sweetlilmre/Dominator-Parts/reference/cam_v2/own_cam_top_v2.jpg

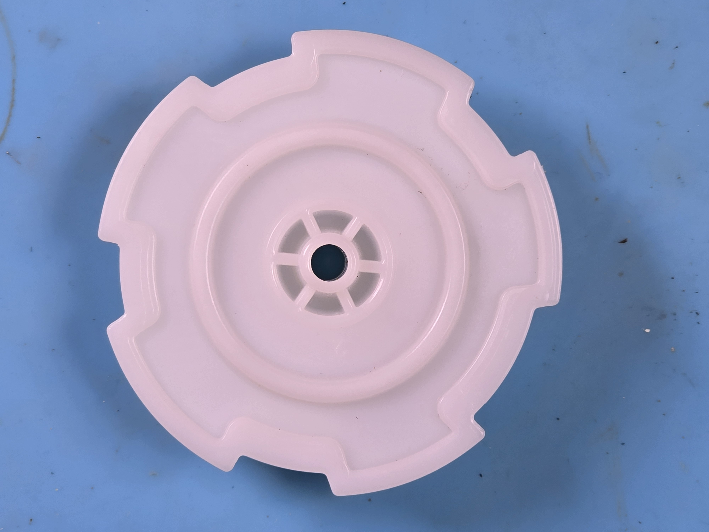
reference/cam_v2/own_cam_top_v2.jpg
