sweetlilmre/Dominator-Parts/reference/cam_v2/own_gear_side_2_v2.jpg

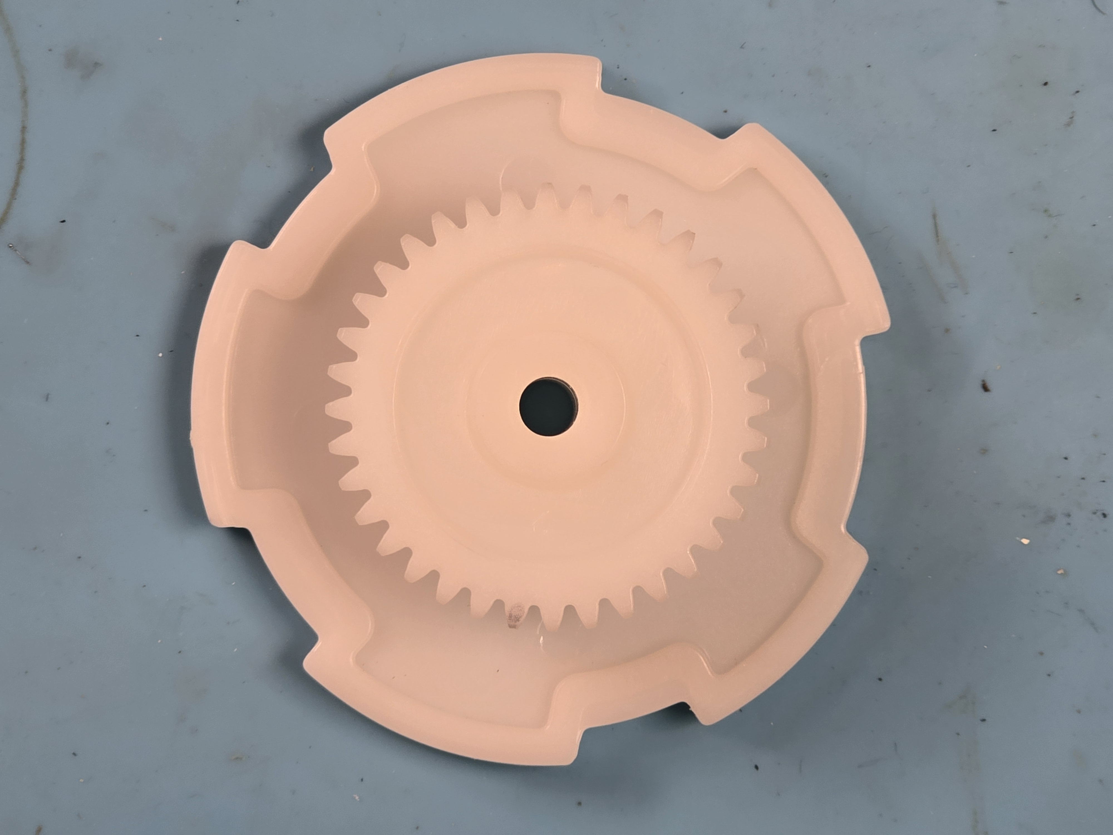
reference/cam_v2/own_gear_side_2_v2.jpg
