sweetlilmre/Dominator-Parts/reference/drive_gears/own_drive_gear_2.jpg

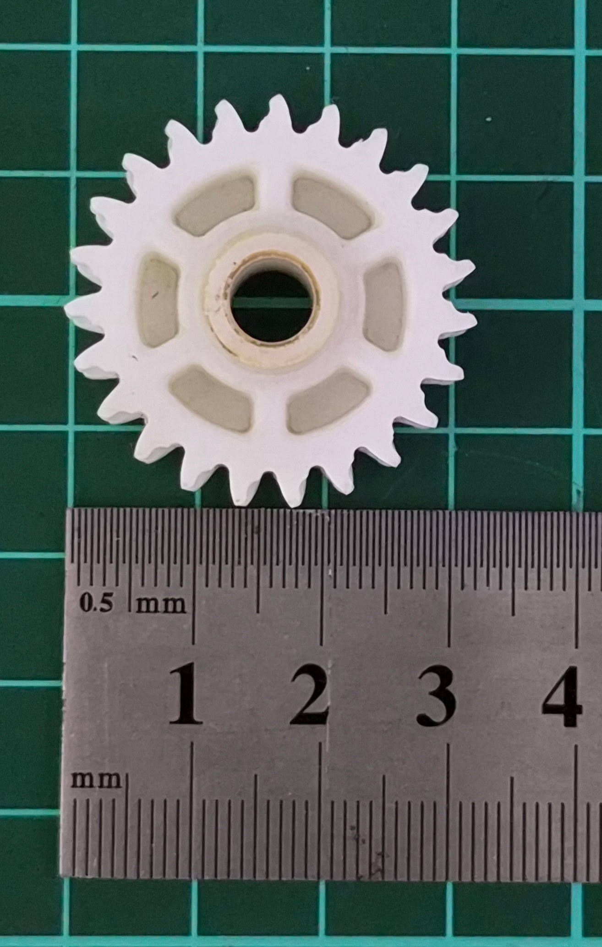
reference/drive_gears/own_drive_gear_2.jpg
