sweetlilmre/Dominator-Parts/reference/drive_gears/own_drive_gear_2_side.jpg

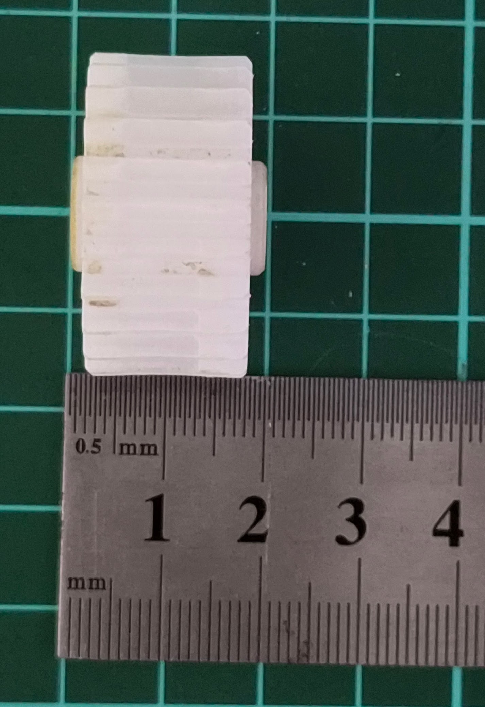
reference/drive_gears/own_drive_gear_2_side.jpg
