sweetlilmre/Dominator-Parts/reference/drive_gears/own_drive_gear_3_top.jpg

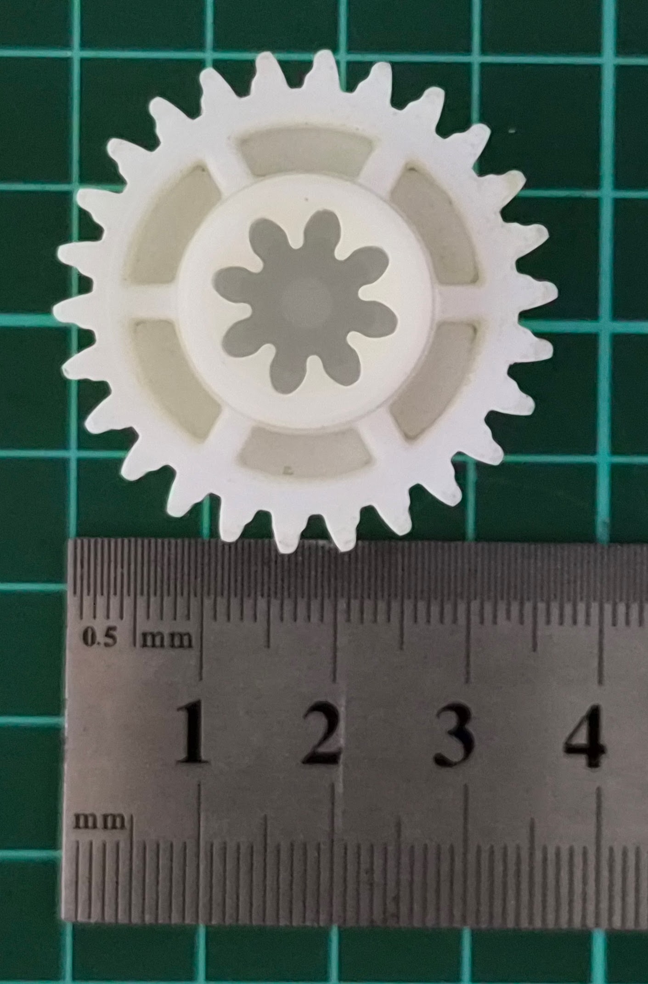
reference/drive_gears/own_drive_gear_3_top.jpg
