sweetlilmre/Dominator-Parts/reference/own_shafts_ruler.jpg

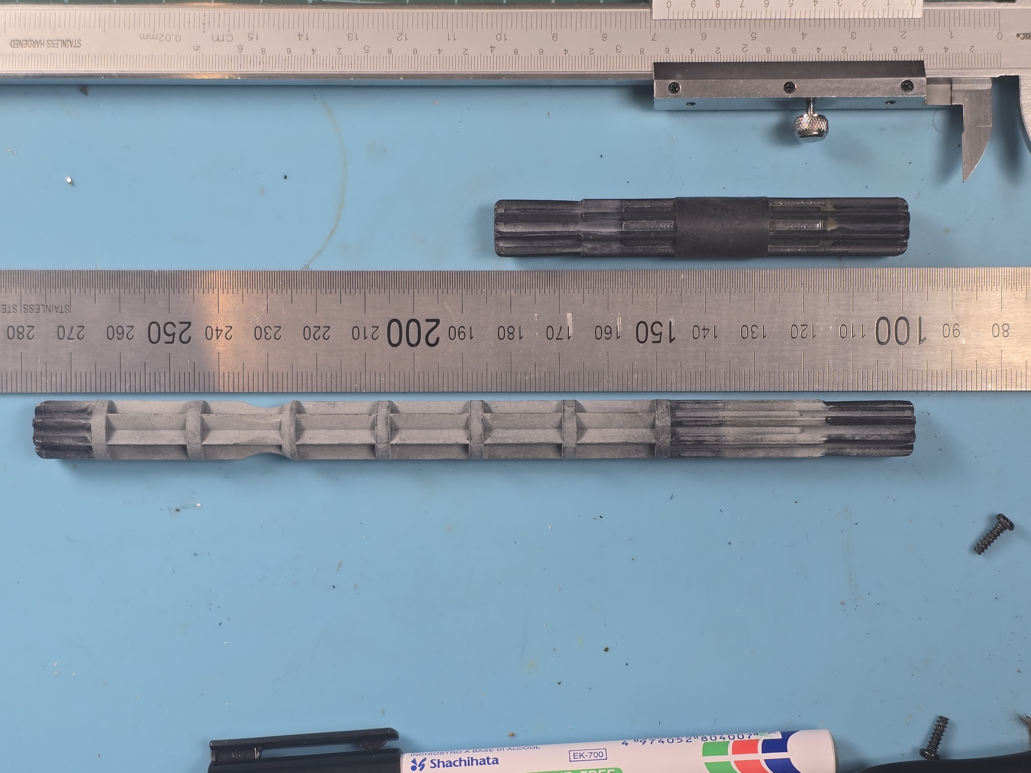
reference/own_shafts_ruler.jpg
