sweetlilmre/Dominator-Parts/renders/shaft_long_flat.png

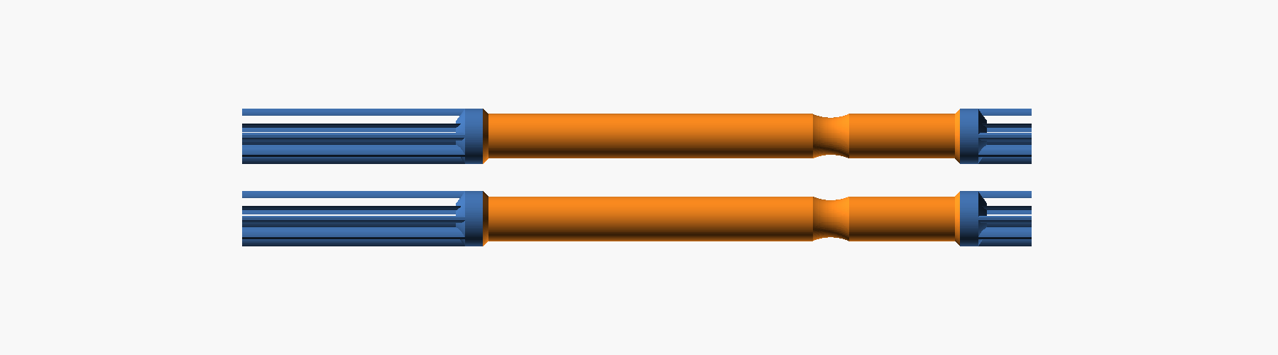
renders/shaft_long_flat.png
