sweetlilmre/Dominator-Parts/renders/shaft_short_end.png

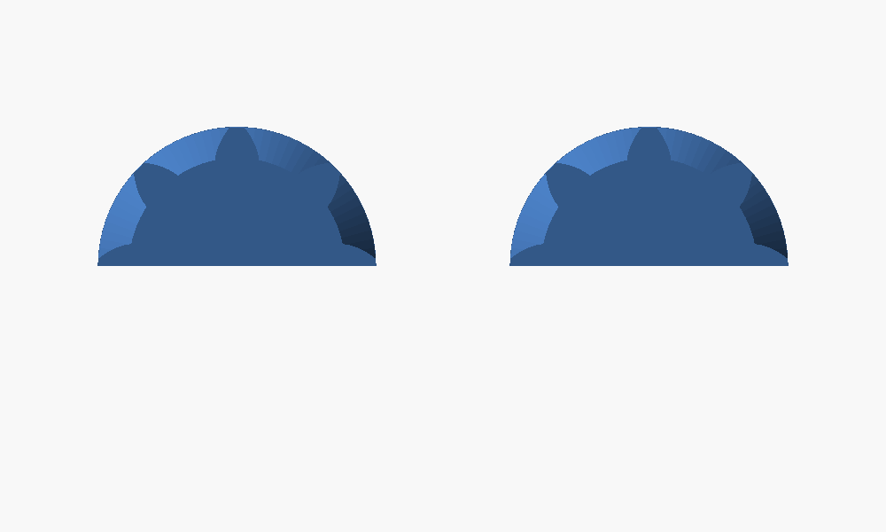
renders/shaft_short_end.png
