sweetlilmre/Dominator-Parts/renders/shaft_short_flat.png

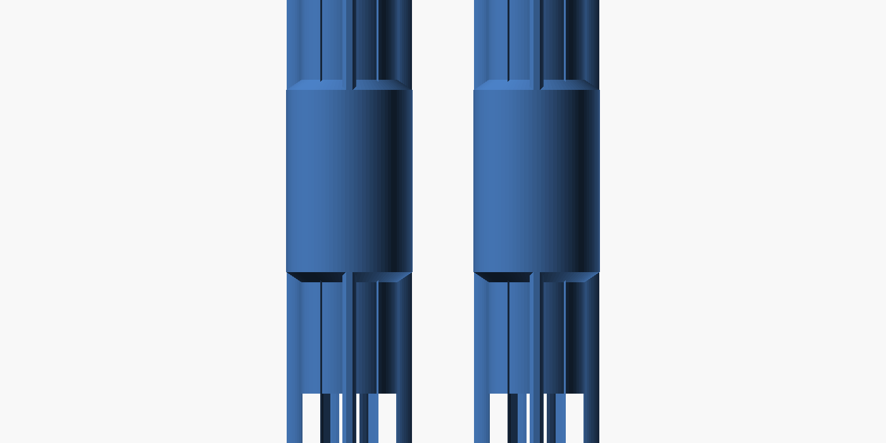
renders/shaft_short_flat.png
