sweetlilmre/Dominator-Parts/stl/dominator_follower.stl

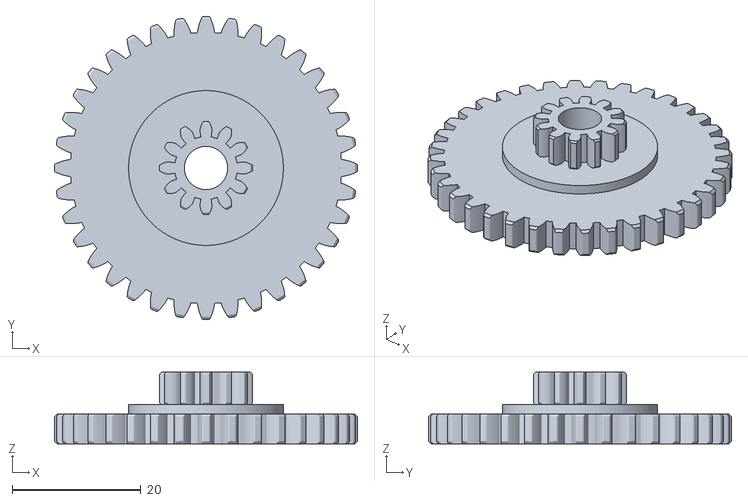
[picture p46: CAD file, 2026-09-06]
stl/dominator_follower.stl
47.0 x 47.0 x 11.1
