sweetlilmre/Dominator-Parts/stl/dominator_washer.stl

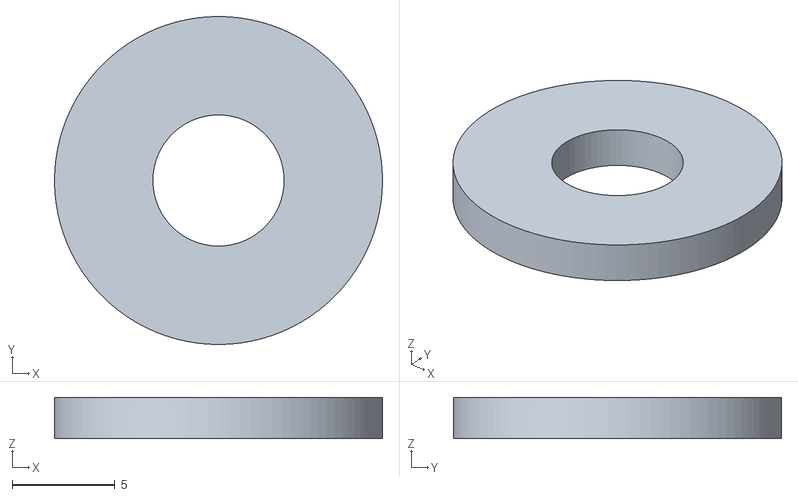
[picture p47: CAD file, 2026-10-06]
stl/dominator_washer.stl
16.0 x 16.0 x 2.00
