sweetlilmre/Dominator-Parts/stl/dominator_cam_v1.stl

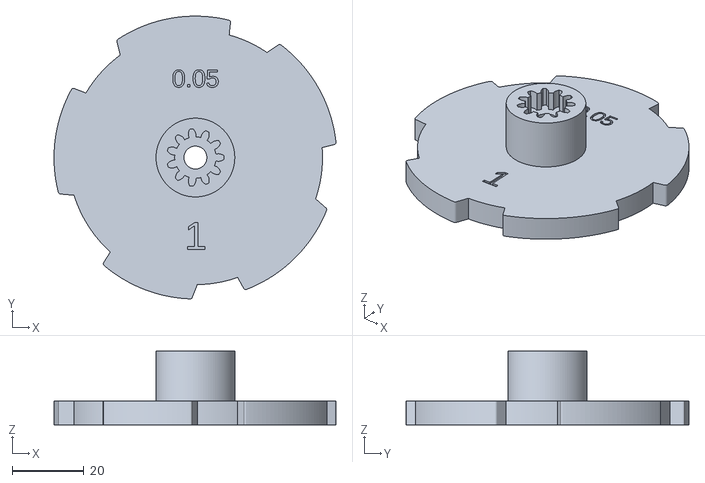
[picture p48: CAD file, 2026-10-06, an earlier design]
stl/dominator_cam_v1.stl
78.8 x 79.0 x 20.6
