sweetlilmre/Dominator-Parts/scad/assembly.scad

// assembly.scad - open this file in OpenSCAD. Use the Customizer panel
// (Window > Customizer) to pick the part and tune every dimension from
// config.scad. Export STLs from here or with render.ps1.
//
//   part = "cam"       flat cam plate with shaft and socket (print as shown)
//   part = "gear"      ring gear with plug, shown plug up for printing
//   part = "washer"    spacer washer
//   part = "reduction_gear"  optional gearbox reduction gear (ring as the gear, plus pinion)
//   part = "assembly"  cam with the gear seated, for checking fit and height
//   part = "shaft_long"   gearbox drive shaft, long
//   part = "shaft_short"  gearbox drive shaft, short
//   part = "drive_gear_1" gearbox drive gear 1, compound 26 T over 19 T
//   part = "drive_gear_2" gearbox drive gear 2, 23 T with a spacer each face
//   part = "drive_gear_3" gearbox drive gear 3, 26 T joining the drive shafts, in two halves
//   part = "cam_rim_modifier"    PrusaSlicer modifier: solid rim band on the cam
//   part = "cam_socket_modifier" PrusaSlicer modifier: solid hub around the cam socket
//   part = "gear_tooth_modifier" PrusaSlicer modifier: solid tooth band on the gear
//   part = "gear_core_modifier"  PrusaSlicer modifier: solid plug on the gear, or pinion on the reduction gear
//   part = "fit_test"  coupon: sockets at several clearances plus loose plugs
//   part = "all"       everything laid out
INVOLUTE_GEAR_NO_DEMO = true;
include <config.scad>
include <cam.scad>
include <cam_gear.scad>
include <reduction_gear.scad>
include <drive_shaft.scad>
include <drive_gear.scad>
include <fit_test.scad>

/* [Part selection] */
part = "all"; // ["all", "cam", "gear", "washer", "reduction_gear", "assembly", "shaft_long", "shaft_short", "drive_gear_1", "drive_gear_2", "drive_gear_3", "fit_test", "cam_rim_modifier", "cam_socket_modifier", "gear_tooth_modifier", "gear_core_modifier"]

module assembled() {
    cam();
    translate([0, 0, shoulder_z()]) cam_gear();
}

if (part == "cam") {
    cam();
} else if (part == "gear") {
    cam_gear_printable();
} else if (part == "washer") {
    spacer_washer();
} else if (part == "reduction_gear") {
    reduction_gear();
} else if (part == "shaft_long") {
    drive_shaft(ds_long);
} else if (part == "shaft_short") {
    drive_shaft(ds_short);
} else if (part == "drive_gear_1") {
    drive_gear_1();
} else if (part == "drive_gear_2") {
    drive_gear_2();
} else if (part == "drive_gear_3") {
    drive_gear_3();
} else if (part == "fit_test") {
    fit_test();
} else if (part == "assembly") {
    assembled();
} else if (part == "cam_rim_modifier") {
    cam_rim_modifier();
} else if (part == "cam_socket_modifier") {
    cam_socket_modifier();
} else if (part == "gear_tooth_modifier") {
    gear_tooth_modifier();
} else if (part == "gear_core_modifier") {
    gear_core_modifier();
} else {
    cam();
    translate([trough_d + 20, 0, 0]) cam_gear_printable();
    translate([trough_d + 20, -(gear_od / 2 + washer_od), 0]) spacer_washer();
    translate([trough_d + 20, gear_od + 8, 0]) reduction_gear();
}

echo(str("gear module = ", gear_module, " mm, pitch dia = ", gear_module * gear_teeth,
         " mm, OD = ", gear_outer_diameter(gear_teeth, gear_module), " mm"));
echo(str("stack: washer ", washer_t, " + plate ", plate_t, " + shaft ", hub_h, " + gear ", gear_thickness,
         " = ", washer_t + plate_t + hub_h + gear_thickness, " mm wall to gear top; plug engages ",
         plug_h, " mm into the hub, socket floor ", hub_h - plug_h - socket_extra,
         " mm above the plate"));
echo(str("cam outer span = ", trough_d + 2 * lobe_height, " mm; spline root dia = ",
         2 * gear_root_radius(spline_teeth, gear_module_from_od(spline_od, spline_teeth, spline_addendum), spline_dedendum),
         " mm vs bore ", bore_d, " mm"));
echo(str("drive gear 1: module ", dg1_module, ", outer ", dg1_outer_teeth, " T at ", dg1_outer_od,
         " mm, inner ", dg1_inner_teeth, " T at ", dg1_inner_od, " mm, height ", dg1_height(), " mm"));
echo(str("drive gear 2: module ", dg2_module, ", ", dg2_teeth, " T at ", dg2_od,
         " mm, body ", dg2_h, " mm, height ", dg2_height(), " mm"));
echo(str("drive gear 3: module ", dg3_module, ", ", dg3_teeth, " T at ", dg3_module * (dg3_teeth + 2),
         " mm, height ", dg3_height(), " mm, sockets ", dg3_short_socket, " + ", dg3_long_socket,
         " mm, wall ", dg3_height() - dg3_short_socket - dg3_long_socket, " mm, ",
         dg3_split ? str("split at z ", dg3_cut_z()) : "one piece"));
echo(str("cam version = ", cam_version, ": lobe height ", lobe_height,
         " mm, ", len(lobes), " lobes"));

// The reduction gear's pinion drives the cam gear, so the two must share a
// module. They are separate parameters on purpose; this is the guard rail.
_mesh_err = abs(rg_pinion_module / gear_module - 1) * 100;
echo(str("mesh check: pinion module ", rg_pinion_module, " vs cam gear ", gear_module,
         " = ", _mesh_err, " percent",
         _mesh_err > 2 ? "  *** WARNING: these will not mesh, check rg_pinion_od / rg_pinion_teeth ***" : " (ok)"));
