sweetlilmre/Dominator-Parts/scad/reduction_gear.scad

// reduction_gear.scad - one of the gearbox reduction gears: a ring, a
// raised plate, a small pinion on top, through bore. The
// ring reads the same as the cam gear today but is a separate part and takes
// its dimensions from the rg_ring_* parameters, so editing the cam gear does
// not reshape this one. The pinion must still mesh with the cam gear, which
// assembly.scad checks. The exact outline of the OEM plate is not known from
// photos; it is modelled as a plain disc. Adjust rg_plate_d / rg_plate_h or
// replace pinion_plate() once you can trace the real one.
// Module library: expects config.scad to be included by the caller.

rg_pinion_module = gear_module_from_od(rg_pinion_od, rg_pinion_teeth);

module pinion_plate() {
    if (rg_plate_h > 0) cylinder(h = rg_plate_h + eps, d = rg_plate_d);
}

module reduction_gear() {
    difference() {
        union() {
            spur_gear(rg_ring_teeth, rg_ring_module, rg_ring_thickness,
                      pa = gear_pressure_angle, backlash = gear_backlash,
                      addendum = gear_addendum, dedendum = gear_dedendum,
                      tip_round = gear_tip_round, chamfer = gear_chamfer);
            translate([0, 0, rg_ring_thickness - eps]) pinion_plate();
            translate([0, 0, rg_ring_thickness + rg_plate_h - eps])
                spur_gear(rg_pinion_teeth, rg_pinion_module, rg_pinion_h + eps,
                          pa = gear_pressure_angle, backlash = gear_backlash, chamfer = 0.3);
        }
        translate([0, 0, -1])
            cylinder(h = rg_ring_thickness + rg_plate_h + rg_pinion_h + 2, d = bore_d, $fn = 64);
    }
}
