sweetlilmre/Dominator-Parts/measure/cam_v2/7_top_lobe_faces_v2.png

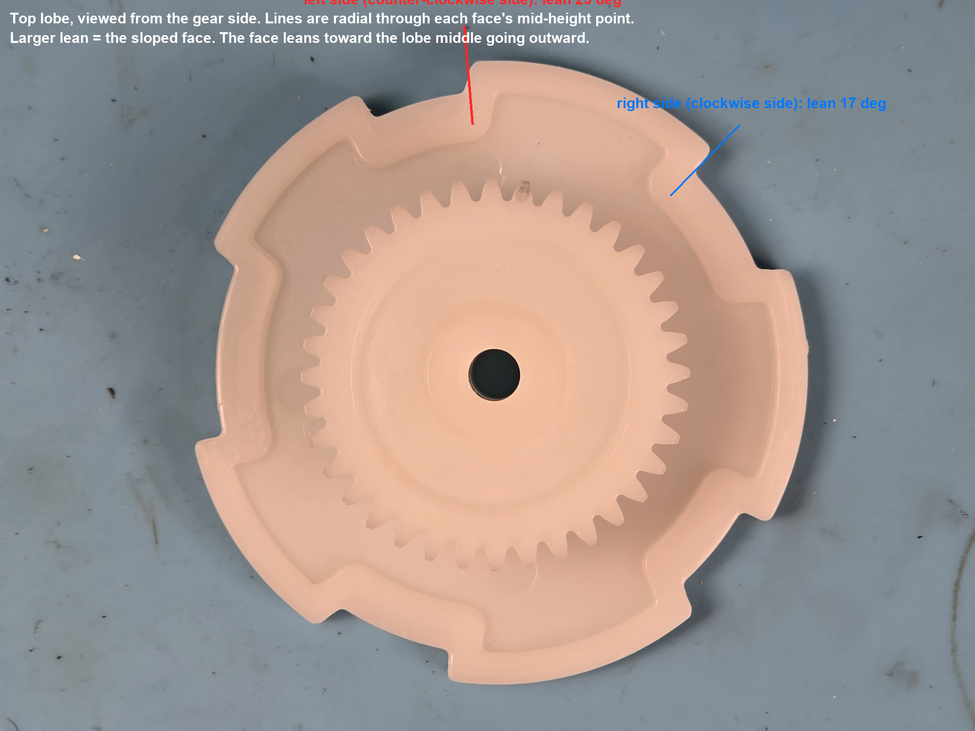
measure/cam_v2/7_top_lobe_faces_v2.png
